EcutAtom336/VFDCLK/MCU/components/my_clock/my_clock.h

#ifndef _MY_CLOCK_H_
#define _MY_CLOCK_H_

#include "cJSON.h"

void my_clock_get_config_json(cJSON *config_json_parent);

void my_clock_analysis_config_json(cJSON *config_json_parent);

void *my_clock_on_create();

void my_clock_on_pause(void *context);

void my_clock_on_resume(void *context);

void my_clock_on_destroy(void *context);

#endif
